kmakise/IndustrialPowerManagement5V5CH3A/MCUproject/Task/Task03.h

#ifndef __TASK03_H
#define __TASK03_H
#include "main.h"

uint32_t getTimeVal(void);
void setTimeVal(uint32_t sec);

uint8_t getTimeState(void);
void setTimeState(uint8_t st);

void Task03Main(void);

#endif /*__TASK03_H*/
